Svenson84/Solax-X1-mini-RS485-WiFi-Stick/CAD/Solax_V3.png

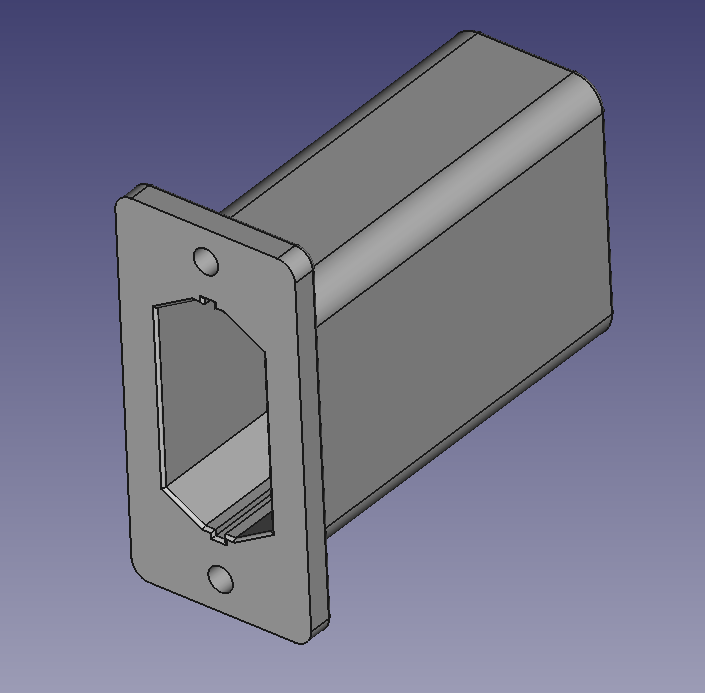
CAD/Solax_V3.png
