Svenson84/Solax-X1-mini-RS485-WiFi-Stick/docs/dongle_05.jpeg

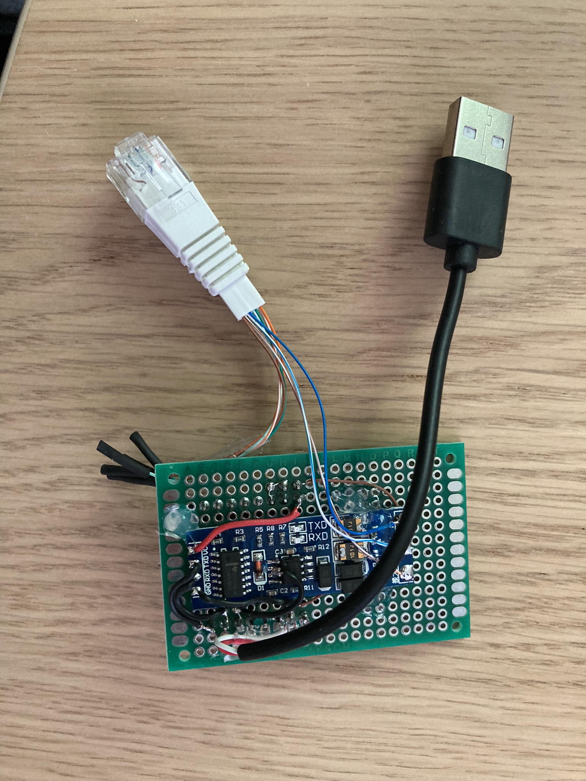
docs/dongle_05.jpeg
