Svenson84/Solax-X1-mini-RS485-WiFi-Stick/docs/housing_01.jpeg

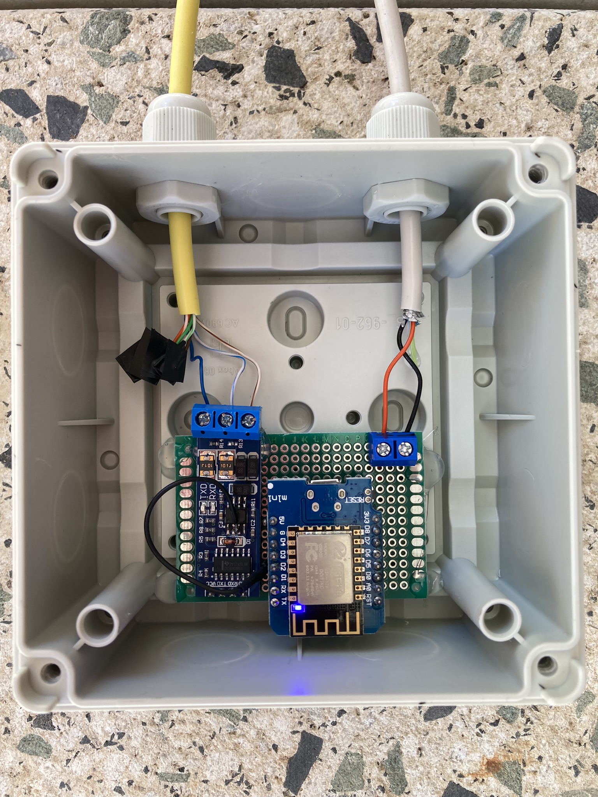
docs/housing_01.jpeg
